amiga-stumpi/funkotto/docs/results/2026-10-10-m4-usb.md

# M4-Konfiguration: USB-Vorbereitung ohne Trägerplatine

Stand 10.10.2026. **Softwareseitig umgesetzt; erster realer USB-Statustest bestanden.**
M0 und aktive M2-Transfers bleiben offen, da noch keine Trägerplatine verfügbar
ist. W5 bleibt ausgelassen. Kein Amiga-Konfigurationsprogramm in diesem Schritt.

## Implementiert

- Gemeinsamer Konfigurationsdispatcher: Fähigkeiten, Status, Scan/Ergebnisse,
  RAM-Profil, Verbinden/Trennen, Speichern/Löschen, asynchrone Auftragsabfrage.
- Separater USB-Modus mit Transportversion 2 und FOC1/API 1.0; bestehende RAW-v1-
  und M2-Diagnoseprotokolle unverändert. Begrenzte COBS-/CRC32-Rahmen, zufällige
  Sitzung, Sequenzen, byteidentischer Replaycache, DTR-/Inaktivitätsende.
- Annahme und Abschluss getrennt; Wiederholung einer verlorenen Antwort löst
  den Auftrag nicht erneut aus. Keine automatische Wiederholung nach Reset oder
  Sitzungsende. CONNECT-OK ist kein LINK_UP-Nachweis; SCAN-OK kein Scanabschluss.
- Python-Werkzeug mit verdeckter Passworteingabe, Fähigkeitenprüfung und JSON-
  Ausgabe ohne Passwort. Keine Passwort-Kommandozeilenoption. Explizites Save
  und Erase; keine automatische Trennung beim Scan.
- Eigenes Ziel `funkotto_m4_usb`, Version `0.1.0-m4-usb`, auf bestehender W4-Basis.
  GPIO-Sperre, W4-Journal und Flash-Speicherlayout erhalten; keine KiCad-Änderung.

## Lokale Nachweise

- Zwölf native C-Testprogramme mit AddressSanitizer/UndefinedBehaviorSanitizer
  bestanden, einschließlich bisheriger WLAN-/Journaltests und der neuen
  Konfigurations-/Konsolenprüfungen. LeakSanitizer lokal wegen eingeschränktem
  /proc-Zugriff deaktiviert; ASan/UBSan bleiben aktiv.
- 29 Python-Unittests bestanden. Zwölf neue Prüfungen verwenden den tatsächlichen
  C-Dispatcher/USB-Parser als Shared Library mit simuliertem WLAN-Service.
  Profil/Connect/Save/Erase, Scan, verzögerter Abschluss/Flashfehler, verlorene
  Antwort, Timeout/Reset ohne erneute Ausführung, BUSY, geänderte Wiederholung,
  Fähigkeiten, CRC/Resynchronisation und Grenzlängen sind abgedeckt.
- C-Prüfungen: Replay vor/nach Auftragsabschluss, Session-/Sequenzfehler,
  Generation/Hidden-SSID, Passwort-Zwischenpufferlöschung, Überlauf, unvollständige
  Rahmen, 50.000 deterministisch erzeugte Streambytes ohne Seiteneffekte.
- Release-Builds für M1, M2 gesperrt, W1/W2, W3, W4 und M4_USB erfolgreich;
  ELF-/UF2-Prüfung für alle sechs Ziele bestanden. M4_USB ohne UART/IP-Stack/
  Parallelport-Aktivierung; flashkritische Funktionen im SRAM. 4-KiB-Core-0-Stack,
  unveränderte zwei Profilsektoren und separate E10-Reservierung geprüft.
- Board-GPIO-/Resetvertrag gegen unverändertes Nutzer-PCB bestanden.

Die Simulation weist keine echte WLAN-Assoziation oder USB-CDC-Timing nach.
DTR, Terminalwechsel und das Zusammenspiel am realen Pico müssen vom Nutzer
geprüft werden. Der neue USB-Modus enthält keine elektrische M0-/M2-Freigabe.
Der exakte Quellstand und die Artefaktprüfsummen stehen im Paketmanifest.
Die [GitHub-CI](https://github.com/amiga-stumpi/funkotto/actions/runs/38085424436)
für Quellstand `e92d982f16d1` ist vollständig erfolgreich abgeschlossen.

## Nutzerprüfung: erster USB-Status (10.10.2026)

Vom Nutzer zurückgemeldet, Windows/COM6, Paket `funkotto-m4-usb-e92d982f16d1`:

```text
python tools/wifi_config.py --port COM6 --report m4-status.json status
```

| Merkmal | Gemeldetes Ergebnis |
| --- | --- |
| Befehlslauf | `stage=M4_USB`, `command=status`, `passed=true` |
| Fähigkeiten | `FOC1`, Version `1.0`, Maske `63`, Payload `128`, Land `DE` |
| WLAN | `LINK_UP`, `error=OK`, `sdk_error=0` |
| Profil | `configured=true`, `stored=true`, `flash_profile=true` |
| Speicher | `storage_state=1` (PROFILE), `flash_ready=true`, `storage_sequence=3`, `storage_error=0` |
| Verbindung | `auto_retry=true`, `attempts=1`, `links=1`, `epoch=2` |
| RSSI | `rssi_valid=true`, `rssi=-46` |
| Scan/Auftrag | `scanning=false`, `sdk_busy=false`, `command_busy=false` |
| USB | `usb_retries=0`, `usb_bad_frames=0` |

SSID `Linux`, MAC `2c:cf:67:e9:c8:b9`, `mac_valid=true`. Scan-Generation,
scan_done und scan_count stehen noch auf 0. Das gespeicherte Profil ist mit
Sequenz 3 weiterhin verfügbar, passend zum zuletzt bestätigten W4-Profil.
Der reale HELLO-/STATUS-Austausch und eine bestehende WLAN-Verbindung sind damit
bestätigt. Neue Konfigurationsänderungen, USB-Scan, Save/Erase und ein separater
M4_USB-Kaltstarttest sind durch diesen lesenden Lauf noch nicht nachgewiesen.
Die Angaben stammen aus der eingefügten Ausgabe; die JSON-Datei selbst wurde
nicht separat hochgeladen oder eingelesen.

## Nutzerprüfung: Disconnect, Scan und Reconnect bestanden (10.10.2026)

Weitere eingefügte Ausgaben aus demselben Paket auf Windows/COM6:

- DISCONNECT: `passed=true`, Job 1 mit `result=OK`; anschließend DISCONNECTED,
  `auto_retry=false`, `epoch=3`. Profil bleibt gespeichert, Sequenz 3.
- SCAN: `passed=true`, Generation 1, `scan_done=1`, fünf Einträge,
  `truncated=false`, `scanning=false`, `sdk_error=0`. Der Scan ist abgeschlossen.
  Zwei Einträge mit SSID `Linux` haben unterschiedliche BSSIDs: Kanal 10,
  RSSI -45, Authwert 5 sowie Kanal 11, RSSI -85, Authwert 7. Das sind getrennte
  BSSIDs, keine doppelte Ausgabe desselben Scan-Eintrags.
- CONNECT: Job 1 mit `result=OK`, `auto_retry=true`, `attempts=2`, `epoch=4`.
  Sofortiger Status CONNECTING, `sdk_busy=true`; eine weitere STATUS-Abfrage
  weiterhin CONNECTING, nun `sdk_busy=false`. `links=1` stammt noch von der
  Verbindung vor DISCONNECT und belegt keinen erfolgreichen Reconnect.
- Alle vier Befehlsläufe melden `passed=true`, `usb_retries=0` und
  `usb_bad_frames=0`; keine Speicherfehler, Profilsequenz unverändert 3.

Eine nachfolgende STATUS-Ausgabe bestätigt den Reconnect: `LINK_UP`,
`error=OK`, `sdk_error=0`, `attempts=2`, `links=2`, `epoch=4`.
RSSI -50 mit `rssi_valid=true`; `sdk_busy=false`, `command_busy=false`.
Profil weiterhin gespeichert, Sequenz 3, `storage_error=0`. Auch diese Abfrage
hat `passed=true`, `usb_retries=0` und `usb_bad_frames=0`.
Damit ist die gesamte Folge Disconnect → Scan → Connect → LINK_UP real bestanden.
Die Zähler zeigen einen zusätzlichen Verbindungsversuch und einen zusätzlichen
Linkaufbau; die genaue Verbindungsdauer wurde nicht gemessen. Während DISCONNECTED/CONNECTING ist
`rssi_valid=false`; der angezeigte RSSI ist dann kein aktueller Messwert.
Jobnummer 1 je Aufruf ist erwartbar, da das Werkzeug jeweils eine neue
USB-Sitzung öffnet. Keine Profiländerung oder Speicheroperation erforderlich.

## Nutzerprüfung: Profileingabe und Verbindung bestanden (10.10.2026)

Der Nutzer hat `set --ssid "Linux"` mit verdeckter WPA2-Passworteingabe,
anschließend CONNECT und STATUS auf demselben Paket/COM6 ausgeführt.

- SET: `passed=true`, Job 1 mit `result=OK`; DISCONNECTED, `configured=true`,
  `auto_retry=false`, `epoch=6`. `stored=true`, Speichersequenz weiterhin 3.
- CONNECT: Auftrag OK, zunächst CONNECTING, `attempts=3`, `epoch=7`.
- STATUS: LINK_UP, `error=OK`, `sdk_error=0`, `attempts=3`, `links=3`, `epoch=7`;
  RSSI -55 mit `rssi_valid=true`. Keine laufenden SDK-/Kommandoaufträge.
- Alle drei Läufe ohne USB-Wiederholungen oder fehlerhafte USB-Rahmen.
  `storage_error=0`, `flash_profile=true`, `flash_ready=true`.

Damit sind die verdeckte Eingabe, SET über USB und die Verbindung mit dem
übergebenen RAM-Profil real bestanden. `stored=true` nach SET ist erwartbar:
Der Service vergleicht RAM-Profil und gespeichertes Profil bytegenau; identische
Daten bleiben als gespeichert markiert. SET selbst schreibt nicht in den Flash.
Dieser Test weist keine Änderung des persistenten Profils nach. Das Passwort
wurde weder zurückgegeben noch ins Repository übernommen.

## Nutzerprüfung: SAVE und Wiederanlauf bestanden (10.10.2026)

Als Antwort auf den SAVE-/Kaltstartablauf wurden drei Ausgaben zurückgemeldet:

- SAVE: `passed=true`, Job 1 mit `result=OK`, `stored=true`, `flash_profile=true`,
  `storage_sequence=3`, `storage_error=0`. Während der Antwort bereits CONNECTING,
  `sdk_busy=true`, `attempts=4`, `links=3`, `epoch=9`.
- Nachfolgender STATUS: LINK_UP, `attempts=4`, `links=4`, `epoch=9`, RSSI -46,
  `rssi_valid=true`. Damit auch Wiederverbindung nach dem SAVE-Ablauf bestätigt.
- Letzter STATUS im angeforderten Kaltstartablauf: LINK_UP, `attempts=1`, `links=1`,
  `epoch=2`, Scan-Generation/scan_done/scan_count wieder 0. Profil `Linux` weiter
  vorhanden und gespeichert, Sequenz 3, `flash_ready=true`, `auto_retry=true`,
  RSSI -45 mit gültigem Messwert. `error=OK`, `sdk_error=0`, `storage_error=0`.
- Alle drei Befehlsläufe: `usb_retries=0`, `usb_bad_frames=0`, `passed=true`.

SAVE mit identischem Profil ist als erfolgreicher, idempotenter Auftrag geprüft;
Sequenz 3 bleibt erwartungsgemäß erhalten. Das ist kein Nachweis eines neuen
Flash-Schreibvorgangs. Die zurückgesetzten Laufzeit-/Scanzähler belegen einen
Neustart mit wiederhergestelltem Profil und erfolgreichem Linkaufbau. Die letzte
Ausgabe wird als Ergebnis des angeforderten Kaltstart-/Autoconnecttests geführt;
Stromunterbrechung und Einschaltzeit wurden nicht separat instrumentiert.

Damit sind HELLO/STATUS, Disconnect, Scan, Connect, SET, idempotentes SAVE und
Wiederanlauf für M4_USB im Nutzerablauf bestätigt. ERASE/Neuanlage über den neuen
USB-Zugang und gezielte Stromausfälle während Flashoperationen bleiben offen;
bestehende W4-Nachweise werden nicht als neue M4_USB-Tests ausgegeben.

## Nächste Schritte

1. Amiga-Konfigurationsclient (68000/V34) mit lokalem Simulationsmodus vorbereiten;
   die bestätigte USB-Basis kann dafür verwendet werden, ohne auf die Platine zu warten.
2. ERASE und Neuanlage über USB bei gewünschtem Löschen separat prüfen; erst damit
   einen neuen persistenten Schreibvorgang über diese Schnittstelle nachweisen.
3. Sobald die Trägerplatine vorliegt, M0 und aktive M2-Tests durchführen und danach
   den Konfigurationsclient an den echten Parallelport anbinden. Die vollständige
   M4-Abnahme einschließlich erweiterter Flash-/Resetprüfungen bleibt offen.

[Plan](../konfigurationsprotokoll-plan.md) ·
[Protokoll](../../protocol/CONFIG.md) · [Anleitung](../../firmware/M4_USB_TEST.md)
