amiga-stumpi/funkotto/docs/results/2026-10-09-m2.md

# M2 – Pico-Transport und Amiga-Diagnose

Stand 09.10.2026: M2 ist **softwareseitig implementiert und lokal geprüft**.
Der Nutzer hat einen erfolgreichen SELFTEST-Lauf auf Amiga 500 mit 68020,
Kickstart 1.3 und Workbench 1.3 zurückgemeldet.
Reale Parallelport-Transfers und Messungen bleiben offen; M2 ist noch nicht
als Hardwaremeilenstein abgenommen.
W5 wurde auf Nutzerwunsch ausgelassen; M0 bleibt vor aktiven Bustests erforderlich.

## Umsetzung

- Eigenes Pico-Ziel `funkotto_m2`, standardmäßig nicht aktivierbar. Separater
  Labor-Build mit zusätzlicher ausdrücklicher USB-Aktivierung; jeder Boot gesperrt.
- PIO/DMA-Transport mit definiertem CIA-Lese-/Schreibhandshake, erstem vorgeladenem
  Lesebyte, OE-Sperre vor Richtungsänderung und Ende erst nach letzter Quittierung.
- Feste 1536-Byte-Diagnoseblöcke, CRC16, geprüfte Längen/Padding, Sitzung,
  Sequenzen, Replay, HELLO/GET_INFO/ECHO/LINK_RESET. Kein Hochgeschwindigkeits-
  Blockmodus, keine Netzwerkintegration und kein SANA-II-Treiber.
- `FunkOttoDiag` als relocierbare HUNK-Datei, reiner 68000-Code, V34-Aufrufe.
  SELFTEST ohne CIA-Zugriff; aktiver RUN nur ausdrücklich, mit Ressourcenbesitz,
  Tick-Zeitgrenzen, Ctrl-C und sicherer Rückgabe. Polling nur im Diagnosetool.
- Keine Änderungen an KiCad, W4-Profilformat oder bestehenden WLAN-Quellen.

## Lokale Prüfungen

- Zehn native C-Testprogramme mit ASan/UBSan bestehen: bisherige M1/WLAN/W3/W4-
  Tests plus M2-Protokoll/Host. Alle 17 bisherigen Python-Tests bestehen.
- Zwei zusätzliche Builds des tatsächlichen Pico-Transportcodes gegen SDK-Fakes
  prüfen Standard-Sperre sowie aktiven Zustandsautomaten: OE-Reihenfolge,
  vorgeladenes erstes Byte, Ressourcen-Rollback, dynamische PIO-Wahl, vorzeitiges
  SEL, Teilantwort, Timeout, ungültiger Request und Rückkehr in den Sperrzustand.
- Die von pioasm 2.2.0 erzeugten Instruktionen laufen in einem kleinen Interpreter:
  1/2/3/1536 Bytes, beide Richtungen, gehaltene Quittung, erstes/letztes Byte,
  FIFO-Stillstand ohne vorzeitige Quittierung oder Datenverlust.
- Die tatsächliche Amiga-HUNK-Datei wird an anderer Basisadresse geladen und
  auf einem Unicorn-68000-Modell ausgeführt. SELFTEST mit 64 ECHOs, RUN mit acht
  ECHOs gegen den nativen Protokollkern über simulierte CIA-Leitungen, belegte
  Ressourcen, Timerkonflikt, fehlender Adapter, Ctrl-C, Argumentprüfung,
  Workbench-Nachrichtenantwort, erhaltene Register/Stack und ungerade Wortzugriffe
  sind geprüft. **OS-Vektoren sind simuliert; dies ist kein OS-1.3-Systemtest.**

Die Tests decken unterschiedliche Grenzen ab: Protokoll, Instruktionsfolge,
Transportcode und 68000-ABI. Sie modellieren weder analoge Signalgüte noch
DMA-Arbitration/CIA-Verzögerungen oder den vollständigen Amiga-Betriebssystembetrieb.

## Build und Auslieferung

Lokale Release-Builds für M1, M2 (gesperrt und Labor), W1/W2, W3 und W4
bestehen. Alle zugehörigen ELF-/UF2-Prüfungen bestehen. Das geprüfte
M2-ZIP enthält 21 vollständig verifizierte Einträge.

Quellstand: [`40d05def4ea8`](https://github.com/amiga-stumpi/funkotto/commit/40d05def4ea85b8c42aa0d0af55377e0d4722755).
Die [GitHub-CI](https://github.com/amiga-stumpi/funkotto/actions/runs/37908258851)
ist **erfolgreich**: Hosttests, Boardvertrag, alle Firmware-Ziele,
M2-Transport-/PIO-Prüfungen, 68000-Build/Emulation, Labor-Build,
ELF-/UF2-Prüfungen, Paketierung und Artefaktupload.

Lokale Auslieferung aus diesem Quellstand:

- Gesperrte `funkotto_m2.uf2`: 71.168 Bytes, SHA256
  `a62d270b127aa08b61c53c9a4ecd9afb6df7499539a3d88ac9f34baff84be049`.
- `FunkOttoDiag`: 13.520 Bytes, SHA256
  `214ef077e72b3c4afdef7f36425c13a74c679219405b4454ac3bfc5e7dd5652a`.

Der letzte HUNK-Lauf nach Eintrag der Quellkennung bestand ebenfalls die
68000-Prüfungen. Eigener Stackverbrauch blieb in den geprüften Pfaden unter
4 KiB; für reale OS-Aufrufe empfiehlt die Anleitung `Stack 8192`.

Pico: unveränderte SDK-/Toolchain-Pins aus `firmware/dependencies.json`.
M2 nutzt 4096 Byte Core-0-Stack, einen dynamisch gewählten reservierten PIO-Block
(30 Instruktionen, ein verwendeter SM) und zwei dynamisch gewählte DMA-Kanäle.
WLAN und Flash-Schreibfunktionen sind im M2-Ziel nicht eingebunden. Die Profile
und der separate E10-Sektor bleiben gemäß ELF-/UF2-Prüfung reserviert.

Amiga: GCC 13.3.0-6ubuntu2~24.04cross1, Binutils 2.42-4ubuntu2.10, freistehender
68000-Build ohne libc, Linux-Runtime oder Amiga-SDK-Binärdateien. Der ELF→HUNK-
Konverter prüft alle Relokationen. OS-Stubs passen Registerargumente und
Zeigerrückgabe an die C-Aufrufkonvention an; Drahtfelder werden auch bei ungeraden
Adressen ausschließlich byteweise geladen/gespeichert.

Das Standard-ZIP enthält ausschließlich die gesperrte M2-UF2, zugehörige
ELF/BIN/MAP-Dateien, `amiga/FunkOttoDiag`, beide Manifeste und Anleitungen/Lizenzen.
Der Paketierer lehnt aktive Laborimages sowie unterschiedliche Quellstände ab
und prüft jeden ZIP-Eintrag bytegenau vor Veröffentlichung.

## Vom Nutzer gemeldeter SELFTEST (09.10.2026)

Zurückgemeldete Ausgabe, für die Lesbarkeit in Zeilen aufgeteilt:

```text
FunkOttoDiag M2 / 68000 / OS 1.3 / polling diagnostic only
source=40d05def4ea8
HELLO session=12340001
ECHO verified count=0x00000040
PASS: local protocol selftest; no CIA access.
```

Der lokale Protokoll-Selbsttest ist damit bestanden: HELLO und 64 geprüfte
ECHOs mit dem ausgelieferten Quellstand. Der SELFTEST verwendet den im Programm
enthaltenen Protokollkern und greift nicht auf CIA, Parallelport oder Pico zu.
`session=12340001` ist die erwartete deterministische Selbsttest-Kennung.

Die Bannerangabe `68000 / OS 1.3` bezeichnet das Buildziel, keine automatische
Erkennung des tatsächlich eingesetzten Systems. Der Nutzer hat das Testsystem
anschließend bestätigt: **Amiga 500, 68020, Kickstart 1.3, Workbench 1.3**.
Damit ist der SELFTEST unter OS 1.3 auf diesem 68020-System bestanden; ein Lauf
auf einer realen 68000-CPU bleibt offen. Der Lauf belegt weder elektrische
Übertragung noch einen bestandenen aktiven M2-Bustest.

## Nächste reale Prüfungen

1. Ergänzender SELFTEST auf einem Amiga mit realer 68000-CPU und OS 1.3.
2. Elektrische M0-Messungen am unveränderten Nutzerboard.
3. Kontrollierter Laborlauf mit aktiver Firmware: zunächst HELLO/64 ECHOs,
   anschließend 100.000 Transfers, Abbruch/Reset in beiden Richtungen und
   Oszillogramme der Übergaben.
4. Erst danach M2-Hardwareabnahme und gemeinsame Integration mit WLAN/Profilen.

[M2-Testanleitung](../../firmware/M2_TEST.md) ·
[Signal-/Rahmenspezifikation](../../protocol/M2.md) ·
[Amiga-Build](../../amiga/diag/README.md)
