amiga-stumpi/funkotto/docs/results/2026-10-09-w4.md

# W4 – Dauerhaftes WLAN-Profil und Autoconnect

Stand 09.10.2026: W4 ist als eigenes Ziel `funkotto_w4` implementiert. Die
W3-Basis (Roh-Ethernet, 1.000 geprüfte Pings und vom Nutzer bestätigte
AP-Wiederverbindung) bleibt erhalten. **Der erste reale W4-Kaltstart mit
automatischer Wiederverbindung ist vom Nutzer ausdrücklich als bestanden
bestätigt.** Der zugehörige Status zeigt ein gültiges gespeichertes Profil
und eine aktive WLAN-Verbindung. Auch der anschließende Löschtest und die
erneute Einrichtung einschließlich Speichern sind durch Nutzerstatus belegt. Die vollständige
Hardwareabnahme bleibt offen.

## Umsetzung

- Zwei reservierte 4-KiB-Sektoren, explizites Format, CRC32, modulare Sequenz
  und gesonderte Commit-Seite. Rücklesen vor Erfolg; identisches Profil ohne
  weitere Flash-Schreibzyklen.
- `wifi save` speichert ausdrücklich. `wifi set` ändert weiter nur RAM.
  Nach Start verbindet das neueste gültige Profil automatisch, ohne USB-Terminal.
- `wifi erase` trennt WLAN, löscht RAM und schreibt zuerst einen Löschdatensatz.
  Alte Flashdaten werden anschließend entfernt. Nach gültigem Lösch-Commit
  kann unterbrochene Bereinigung kein altes Profil aktivieren; Boot setzt sie fort.
- Unbekanntes Format und mehrdeutige Sequenzen werden ohne Autoconnect gemeldet.
  Explizites Löschen erlaubt eine neue Einrichtung. Leerer/beschädigter Speicher
  führt nicht zu einer Bootschleife.
- Core 1 schreibt erst nach WLAN-Deinit, DMA-Ruhe und Prüfung der Bussperre.
  SDK-Multicore-Lockout ist auf beiden Kernen initialisiert; kein geteilter
  Lock wird während Flashoperationen gehalten. Flash-Callback, SDK-Schreib-/
  Löschfunktionen und Lockout-Handler werden im ELF als SRAM-Code geprüft.
- Zusätzlicher Status trennt gespeichertes Profil von abweichendem RAM-Profil.
  Passwörter werden nicht ausgegeben; Speicherung ist unverschlüsselt.
- M1, W1/W2 und W3 bleiben separat baubar. Hardwaredateien unverändert.

## Prüfungen

Hosttests verwenden ASan/UBSan. Neben den bisherigen fünf C-Testprogrammen
kommen Journal-, Flash-Guard-, W4-Service- und W4-Parser-Tests hinzu.
Das Journal wird bei **13.314 Byte-Grenzen** unterbrochen: 4.609 Positionen beim
Ersetzen eines Profils und 8.705 beim Löschen einschließlich Bereinigung.
Zusätzlich werden Erstinstallation in 16-Byte-Schritten, CRC-/Commit-Korruption,
Schemafehler, Sequenzüberlauf/Mehrdeutigkeit, Rücklesefehler und Idempotenz geprüft.

Service-Tests verwenden den tatsächlichen WLAN-Service gegen SDK-/Flash-Fakes:
Speichern, geändertes RAM-Profil, Wiederverbindung, Boot-Autoconnect, Löschen,
Fortsetzung unterbrochener Bereinigung und Schreibverbot ohne Ruhefreigabe.
Backend-Tests prüfen Kernnummer, Bussperre, Opferkern-Initialisierung, DMA-Status,
SRAM-Datenquelle, zulässige Offsets/Seiten und fehlgeschlagenen SDK-Eintritt.
Die bisherigen 17 Python-Tests prüfen weiterhin Rohtransport und Paketierung.

Die Simulation bildet byteweise unterbrochenes NOR-Löschen/Programmieren ab,
keine reale Unterspannung oder beliebige physische Flashschäden. Unterbrechung
vor gültigem Commit kann den alten Stand erhalten; erst bestätigte Befehle sind
als abgeschlossen zu behandeln. Ein SDK-Fehler nach ausgeführtem Callback kann
bereits einen neuen gültigen Datensatz hinterlassen; der Status wird neu geladen.

## Lokales Build-Ergebnis

Alle neun nativen C-Testprogramme mit ASan/UBSan und alle 17 Python-Tests
bestehen. Release-Builds für M1, W1/W2, W3 und W4 bestehen mit der festgelegten
Toolchain und den unveränderten SDK-Pins. Die vier ELF-/UF2-Prüfungen bestätigen
Profil-/E10-Reservierung und fehlende UART-Einbindung; WLAN-Ziele enthalten kein
lwIP. W4 prüft zusätzlich die Flash-kritischen Funktionen im SRAM.
Hardware-Pinvertrag und unverändertes Nutzer-PCB stimmen überein.
Das W4-ZIP enthält 22 bytegenau verifizierte Einträge. Ein realer Pico-Flashvorgang
wurde in dieser Entwicklungsumgebung nicht ausgeführt.

Firmware-Quellstand:
[`229dfaacaf10`](https://github.com/amiga-stumpi/funkotto/commit/229dfaacaf108cbaa65ef3642edf518aa49c6b15).
[GitHub-CI](https://github.com/amiga-stumpi/funkotto/actions/runs/37902238647)
ist **erfolgreich**: Hosttests, Hardwarevertrag, alle vier Firmware-Builds,
ELF-/UF2-Prüfungen, Paketierung und Artefaktupload.

Lokale W4-UF2 aus diesem Quellstand: 595.456 Bytes, SHA256:
`386412f41eb851570c319d267292e420ce99cb8bfcce979476165ac4636550fe`.
Der separate Download und die UF2 im ZIP werden bytegenau verglichen.

## Erster realer W4-Status (09.10.2026)

Vom Nutzer übermittelte Statusfelder (MAC und SSID hier ausgelassen):

```text
wifi=LINK_UP error=OK sdk_error=0 configured=1 stored=1 auto_retry=1 sdk_busy=0
rssi_valid=1 rssi=-37 attempts=3 links=1 epoch=6 retry_at_ms=0
last_link_error=-1 failed_attempt=2
storage=PROFILE storage_error=0 flash_profile=1 flash_ready=1 storage_seq=1
```

- `storage=PROFILE`, `flash_profile=1` und `storage_seq=1` melden einen gültigen
  gespeicherten Profildatensatz. `stored=1` bestätigt, dass das aktuelle RAM-Profil
  mit diesem Datensatz übereinstimmt. Es wird kein Speicherfehler gemeldet.
- `LINK_UP`, `error=OK` und gültiger RSSI bestätigen die aktive WLAN-Verbindung.
  Nach zwei fehlgeschlagenen Versuchen gelang der dritte Verbindungsversuch.
- `last_link_error=-1` (`JOIN_FAILED`) und `failed_attempt=2` sind historische
  Diagnosewerte des zweiten Versuchs, kein aktueller Verbindungsfehler.
- Der Nutzer hat anschließend ausdrücklich bestätigt: „Ja, der Kaltstart mit
  automatischer Wiederverbindung ist bestanden“. Damit ist der erste Kaltstart
  nach vollständigem Stromverlust ohne geöffnetes Terminal als bestanden
  dokumentiert: Das gespeicherte Profil wurde geladen und WLAN automatisch
  wieder verbunden. Grundlage sind die Statusausgabe und die Nutzerbestätigung;
  eine Serie mehrerer Kaltstarts ist damit noch nicht belegt.

## Löschtest und erneute Einrichtung (09.10.2026)

Als Antwort auf den Testablauf `wifi erase`, Erfolg abwarten, stromlos machen,
neu starten und Status prüfen übermittelte der Nutzer:

```text
wifi=UNCONFIGURED error=OK configured=0 stored=0 auto_retry=0
attempts=0 links=0 epoch=0
profile_ssid_len=0 last_link_error=0 failed_attempt=0
storage=DELETED storage_error=0 flash_profile=0 flash_ready=1 storage_seq=2
```

Damit ist der Löschtest im beschriebenen Neustartablauf bestanden: kein geladenes
Profil, kein automatischer Verbindungsversuch und kein Speicherfehler.
`DELETED` bezeichnet den gültigen Löschdatensatz, dessen Sequenz gegenüber dem
vorherigen Profil von 1 auf 2 gestiegen ist.

Die anschließende erneute Einrichtung und Verbindung gelang beim ersten Versuch:

```text
wifi=LINK_UP error=OK configured=1 stored=0 auto_retry=1
rssi_valid=1 rssi=-39 attempts=1 links=1 epoch=3
storage=DELETED storage_error=0 flash_profile=0 flash_ready=1 storage_seq=2
```

Das neue Profil liegt an diesem Punkt erwartungsgemäß nur im RAM. `wifi set`
und `wifi connect` überschreiben den Löschdatensatz nicht. Auf
`wifi command=3 result=OK` folgt eine weitere vom Nutzer übermittelte Statusausgabe:

```text
wifi=LINK_UP error=OK sdk_error=0 configured=1 stored=1 auto_retry=1
rssi_valid=1 rssi=-47 attempts=1 links=1 epoch=2 retry_at_ms=0
last_link_error=0 failed_attempt=0
storage=PROFILE storage_error=0 flash_profile=1 flash_ready=1 storage_seq=3
```

Damit ist auch das erneute Speichern nach dem Löschen bestätigt: gültiges
Flashprofil, Übereinstimmung mit dem aktiven RAM-Profil und kein Speicherfehler.
Die Folge Profil (Sequenz 1), Löschdatensatz (2), neues Profil (3) ist durch die
Statusausgaben belegt. WLAN ist beim ersten Versuch verbunden. Die geänderte
`epoch` allein wird nicht als zusätzlicher Kaltstartnachweis gewertet.

Die grundlegende W4-Funktionsprüfung auf dem Pico ist damit bestanden:
Speichern, bestätigter Kaltstart mit Autoconnect, Löschen im beschriebenen
Neustartablauf sowie erneutes Einrichten, Verbinden und Speichern.

Wiederholte Kaltstarts, Profilerhalt beim Firmwareupdate und unterbrochene
Flashoperationen auf realer Hardware bleiben offen.

## Hardwareabnahme

[W4-Testablauf](../../firmware/W4_TEST.md): neu konfigurieren, `wifi save`,
auf `result=OK` warten, vollständiger Stromverlust, Start ohne geöffnetes Terminal,
`wifi status` prüfen und Rohpakettest wiederholen. Danach `wifi erase` und
Neustart ohne Profil prüfen. Zunächst drei Kaltstarts; weitergehende Abnahme
100 Kaltstarts, fehlender AP, Update-Erhalt sowie unterbrochene Flashoperationen.

SANA-II, aktive Parallelport-Kommunikation, elektrische M0-Abnahme und
Langzeit-/Latenzuntersuchung bleiben separate Schritte. Die Firmware hält
`bus_locked=1` und `output_mask=0x00700000`.

[Format und Sicherheitsmechanismus](../../firmware/PROFILE_FORMAT.md).
