amiga-stumpi/funkotto/docs/results/2026-10-09-w3.md

# W3 – Implementierung und Prüfstand, 09.10.2026

W3 ist als eigenes Firmwareziel `funkotto_w3` implementiert. Die bisherige
W1/W2-Firmware bleibt separat baubar. **Der erste echte ARP/ICMP-Test am Pico
ist am 09.10.2026 bestanden:** Der Nutzer hat unter Windows über COM6 zwölf
geprüfte Echo-Antworten ohne Paketverlust zurückgemeldet. Der anschließende
1.000-Ping-Lauf ist ebenfalls bestanden und anhand von JSON und PCAP geprüft.
AP-Ausfall mit Wiederverbindung und anschließend erneutem Pakettest wurde
vom Nutzer ebenfalls als erfolgreich bestätigt. Langzeitbetrieb und weitere
Belastungstests bleiben offen.

## Änderungen

- Je acht feste TX/RX-Puffer à 1600 Bytes, maximal 1514 Ethernet-Bytes ohne FCS.
- TX-Quell-MAC-Prüfung, Ethernet-II-Prüfung und Nullpadding auf 60 Bytes.
- Core 1 besitzt CYW43 inklusive Sendefunktion; RX kopiert vor Callback-Ende.
- Explizite BUSY-/Drop-/Abbruchzähler, FIFO-Reihenfolge und getrennte Lebensdauer
  von Warteschlange, SDK-Aufruf und abgeholtem TX-Abschluss.
- Link-/Sitzungswechsel bereinigen alte Aufträge. Eine verspätete SDK-Rückkehr
  kann keinen neuen Slot überschreiben. SDK-Erfolg ist keine Zustellbestätigung.
- USB-Testmodus `raw on`: COBS, CRC32, Sitzungsschlüssel, Sequenz und gespeicherte
  Antwort für sichere Wiederholung. DTR Low kehrt zur normalen Konsole zurück.
- Python-Werkzeug für freie Test-IP, ARP, ICMP mit Nutzdatenprüfung, PCAP und JSON.
- W3 in CI, ELF/UF2-Manifest und ZIP-Paketierung aufgenommen. ZIP wird vollständig
  im Speicher abgeschlossen, inhaltlich geprüft, atomar geschrieben und erneut
  bytegenau verifiziert; manifestwidrige Artefakte werden nicht verpackt.

## Automatisierte Prüfungen

Native C-Tests mit AddressSanitizer/UndefinedBehaviorSanitizer:

- Bisherige M1-, WLAN-Parser-/Zustandsautomaten- und echte Service-Tests.
- W3-Pufferbesitz nach Änderung des Eingabepuffers, Mindest-/Maximallänge,
  volle TX-/RX-Ringe, wiederholter Ringumlauf, Padding und FIFO-Reihenfolge.
- Linkverlust, Epochenwechsel, neue USB-Sitzung und verspäteter Sendefertigmeldung.
- CRC-Testvektor, COBS-Grenzlängen, falsche CRC, Session/Sequenzfehler,
  identische Wiederholungen vor/nach TX-Abschluss sowie RX-Wiederholung.
- Übergroßer Datenstrom und 200.000 deterministisch erzeugte Störbytes mit
  anschließender erfolgreicher Resynchronisation.
- Tatsächlicher W3-Service gegen SDK-Fake: TX-Aufruf ohne gehaltene Sperre,
  reentrant aufgerufener RX-Callback, Kopierdauer und Linkverlust vor Sendung.

Python-Tests prüfen das PC-Werkzeug direkt gegen die kompilierte C-Protokoll- und
Pufferimplementierung: abgeschnittene HELLO/TX/RX-Antworten werden wiederholt,
ohne doppelte Sendung/RX-Entnahme. Hinzu kommen ARP, ICMP-Prüfsummen, Adressen,
Sequenzen/Nutzdaten, Konflikterkennung, ARP-Antworten und PCAP-Aufbau.

## Build-Ergebnis

Lokaler Release-Build für Pico 2 W / RP2350 Arm mit den festgelegten SDK-/Treiber-
und Toolchain-Versionen erfolgreich. Alle fünf nativen Testprogramme mit ASan/UBSan
und 17 Python-Tests bestehen; Hardware-Pinvertrag stimmt mit dem Nutzer-PCB überein.
M1-, W1/W2- und W3-ELF/UF2-Prüfung bestätigen die getrennten Flashbereiche und
fehlende UART-Einbindung. W3 bindet weder lwIP noch DHCP ein. Der SDK-pbuf-Zweig
wird ausschließlich durch einen Fehler-Guard erfüllt; alle Sendungen verwenden
`is_pbuf=false`. Es gibt keine SDK-Quelländerungen.

Der eigene Release-Quellcode wird mit Warnungen als Fehler gebaut. Core 0 behält
seinen 4-KiB-Stack in der Scratch-Bank; Paketarbeitsbereiche sind statisch.
Core 1 behält den expliziten 8-KiB-Stack. Artefaktgrößen, Hashes und konkreter
Quellcommit stehen im mitgelieferten Manifest.

Firmware-Quellstand: [`b09aa6182ef8`](https://github.com/amiga-stumpi/funkotto/commit/b09aa6182ef814f4965a1bd229d03698d7e88c7d).
[GitHub-CI für diesen Commit](https://github.com/amiga-stumpi/funkotto/actions/runs/37897967381)
ist **erfolgreich**: Hardwarevertrag, Hosttests, alle drei Firmwareziele,
Artefaktprüfungen, ZIP-Paketierung und Upload.

Die lokal aus diesem Quellstand gebaute W3-UF2 ist 585.728 Bytes groß, SHA256:
`b655c34715b19611c58d3c50cd730697e5d13c5ff06ceb72f457ee2298a72ab8`.
Das ZIP enthält UF2, ELF, Map, BIN, Manifest, PC-Werkzeug, Anleitungen und
Lizenzhinweise. Alle 20 Einträge werden bytegenau geprüft.

## Erster realer W3-Test – Nutzerrückmeldung vom 09.10.2026

Getestet mit dem bereitgestellten Paket `funkotto-w3-b09aa6182ef8` unter Windows,
USB-Port COM6. Grundlage ist die vom Nutzer übermittelte Konsolenausgabe;
die erzeugten Dateien `w3.pcap` und `w3.json` wurden nicht separat eingesehen.

| Prüfung | Ergebnis |
| --- | --- |
| USB HELLO / STATS | erfolgreich, gültige Stations-MAC, Link aktiv |
| WLAN-Link-Epoche | unverändert 3 während beider Läufe |
| ARP-Auflösung | Gegenstelle antwortet |
| ICMP-Echo | 12 gesendet, 12 empfangen, 0 verloren |
| ICMP-Nutzdaten | 0, 56, 512, 1472 Bytes, jeweils dreimal; alle `verified=1` |
| Maximaler Frame | 1514 Bytes ohne FCS / IPv4-MTU 1500 erfolgreich |
| TX | 16 eingereiht, 16 vom SDK angenommen, 0 Fehler/Abbrüche/BUSY/ungültige Frames |
| RX während Pakettest | 16 zusätzlich eingereiht (Zähler 1 → 17), 0 Überläufe/ungültige Frames |
| USB | 0 Wiederholungen; Firmware: 0 fehlerhafte Frames und 0 Sequenzfehler |
| Puffer am Testende | TX 0, RX 0; bisherige Höchstbelegung jeweils 1 |

Die 16 TX-Frames passen zu drei ARP-Adressproben, einer ARP-Auflösung und zwölf
ICMP-Anfragen. Die Echo-Prüfung belegt den funktionierenden Rohdatenpfad in
beide Richtungen einschließlich Ethernet-Mindestlänge und MTU-Grenze. Der
PC sendet kurze Frames bereits auf 60 Bytes aufgefüllt; der zusätzliche
Padding-Zweig der Firmware wurde damit nur in den automatisierten Tests geprüft. Der
vorherige reine Statusaufruf hatte noch keine TX-Pakete gesendet; sein
`passed=true` allein wäre kein LAN-Paketnachweis gewesen.

Gemeldete RTT: 0 bis 78 ms, Mittelwert ca. 33,83 ms. Sie enthält PC, USB und WLAN
und ist kein Amiga-Durchsatzwert. Die sichtbare Zeitquantisierung und `0.00 ms`
erlauben keine Aussage über die tatsächliche minimale Funklatenz.

### Einmaliger Host-Zähler `usb_bad_frames=1`

Beide Aufrufe melden hostseitig genau einen fehlerhaften Frame, ohne Wiederholung.
Die Ursache lässt sich aus dem Übergang zum Binärmodus reproduzieren:
`main_wifi.c` gibt vor dessen Aktivierung die ASCII-Zeile `RAW v1; ...` aus;
`wifi_diag.py` führt diese Textbytes bis zum ersten Null-Delimiter zunächst dem
COBS-Decoder zu. Dabei erhöht es seinen Sammelzähler `bad_frames`. Dieser zählt
auch ungültige Text-/Framingdaten, nicht ausschließlich CRC-Fehler.

Ein lokaler Nachstelltest mit dieser Begrüßung vor dem tatsächlichen
C-Protokollcode erzeugt genau `usb_bad_frames=1`, `usb_retries=0` und gültige
HELLO-/STATS-Antworten. Somit ist der hier beobachtete einzelne Startzähler
kein Hinweis auf verlorene Ethernet-Pakete. Weitere Fehler während der Sitzung
wären gesondert zu untersuchen. Eine getrennte Zählung der Startbegrüßung ist
eine mögliche spätere Verbesserung des PC-Werkzeugs; keine neue Firmware ist
für diesen erfolgreichen Test erforderlich.

`rx_inactive=127` zählt vor dem aktiven Pakettest verworfene Frames und bleibt
währenddessen unverändert. `rx_flushed=1` passt zum beim ersten Statusaufruf
wartenden RX-Frame, der beim Beenden jener Sitzung entfernt wurde.

## Reale Folgeprüfung – 1.000 Pings, 09.10.2026

Der Nutzer hat `w3-1000.json` und `w3-1000.pcap` bereitgestellt. Beide Dateien
wurden vollständig gelesen. Der PCAP-Container ist vollständig: 2.054 Ethernet-
Datensätze ohne abgeschnittene Records oder gekürzte Frames. Der Mitschnitt
umfasst rund 32,786 Sekunden einschließlich ARP-Vorlauf; damit ist dies ein
wiederholter Funktionstest, noch kein stundenlanger Dauerlauf.

| Prüfung | Ergebnis |
| --- | --- |
| JSON-Gesamtergebnis | `passed=true`, 1.000 gesendet, 1.000 empfangen, 0 verloren |
| PCAP-Echo-Paare | 1.000 Anfragen und 1.000 passende Antworten, Sequenzen 1–1.000 |
| Duplikate | keine doppelten Echo-Anfragen oder -Antworten |
| Nutzdatenlängen | 0, 56, 512 und 1472 Bytes, jeweils 250 Paare |
| Inhaltsprüfung | Alle Paare: MAC-/IP-Adressen, IPv4-/ICMP-Prüfsummen, Kennung, Sequenz und exakte Nutzdaten korrekt |
| Framegrenzen | TX-Länge jeweils `max(60, 42 + ICMP-Nutzdatenlänge)`; maximal 1514 Bytes ohne FCS |
| TX-Zählerdifferenz | +1.004 eingereiht, +1.004 erfolgreich: drei ARP-Probes, eine ARP-Auflösung, 1.000 Echo-Anfragen |
| RX-Zählerdifferenz | +1.049 eingereiht; zusätzlich ein beim Start wartender Frame; 1.050 RX-Records im PCAP |
| TX-/RX-Fehler | kein TX-Fehler, Abbruch, BUSY, ungültiger Frame oder RX-Überlauf |
| Link | aktiv; Epoche unverändert 3 |
| Puffer | zum Ende beide leer; Höchstbelegung TX 1 / RX 2 von jeweils 8 |
| USB | keine Wiederholung, keine Firmware-Framing-/Sequenzfehler; bekannter Host-Startzähler weiterhin 1 |

PCAP und Bericht stimmen bezüglich TX-/RX-Anzahl überein. Die zusätzlichen
RX-Pakete neben den Echo-Antworten sind im Mitschnitt vorhanden und stellen
keinen Verlust oder zusätzliche Ping-Antworten dar. `rx_inactive` und
`rx_flushed` ändern sich während des Laufs nicht.

### Laufzeiten und Ausreißer

Der JSON-Bericht nennt eine vollständige RTT von durchschnittlich **29,5 ms**,
maximal **1.000 ms**. Die PCAP-Zeitdifferenz vom erfassten TX-Frame zur passenden
Antwort beträgt im Mittel 17,112 ms, Median 12,565 ms, 95. Perzentil 31,992 ms
und 99. Perzentil 57,105 ms (Perzentile nach aufsteigender Rangposition).
Die größten Differenzen sind:

| Echo-Sequenz | ICMP-Nutzdaten | PCAP-Zeitdifferenz |
| --- | --- | --- |
| 872 | 1472 Bytes | 985,263 ms |
| 887 | 512 Bytes | 613,995 ms |
| 987 | 512 Bytes | 301,076 ms |

Auch diese Antworten kamen korrekt und innerhalb des Testzeitlimits an.
Die Ausreißer sind ein offener Messpunkt, kein Paketverlust. Die Ursache lässt
sich hier nicht zwischen PC-Scheduling, USB, WLAN und Gegenstelle aufteilen.
PCAP-TX wird erst nach SDK-Annahme erfasst, während die JSON-RTT schon vor dem
USB-Sendeauftrag beginnt; die Messwerte sind daher nicht direkt gleichzusetzen.
Zusätzlich verwenden die beiden Messungen unterschiedliche Host-Zeitquellen.
Weder der Mittelwert noch `0.00 ms` im JSON sind eine reine Funklatenz oder ein
Amiga-Durchsatzbenchmark. Der Mitschnitt stammt vom USB-Testclient, nicht von
einer unabhängigen LAN-Gegenstelle.

### Zuordnung der geprüften Originaldateien

- `w3-1000.json`, SHA256:
  `c324d77cfaf65e0e130c4af29604b158a7778b21eaa30404343dd031858b456f`
- `w3-1000.pcap`, SHA256:
  `ae9c1cda8e5bb1ca08cea1e67dd8991373a99349f6ddb4711513dde2380c7df4`

Die Originaldateien werden durch diese Dokumentation nicht verändert.

## AP-Ausfall und Wiederanlauf – Nutzerrückmeldung vom 09.10.2026

Auf den angeleiteten Test (AP während des Pakettests ausschalten, wieder
einschalten, auf `LINK_UP` warten und den Pakettest in einer neuen Sitzung
starten) hat der Nutzer mit „das hat funktioniert“ geantwortet.
Damit sind AP-Ausfall, Wiederverbindung und anschließender erneuter Paketbetrieb
als erfolgreiche Nutzer-Hardwareprüfung dokumentiert. Für diesen zusätzlichen
Versuch wurden keine neuen Logs, JSON-Berichte oder PCAP-Dateien übermittelt;
Reaktionszeiten, genaue Fehlerausgabe, Paketanzahl und Zählerverläufe sind daher
nicht separat verifiziert. Die zuvor geprüften 1.000er-Dateien stammen aus dem
ungestörten Lauf und werden nicht als Mitschnitt des Ausfalltests gewertet.

## Grenzen und nächster Schritt

Der reale bidirektionale Basisnachweis und der 1.000-Ping-Test sind erbracht;
der Ausfall-/Wiederanlauftest ist durch den Nutzer bestätigt. Damit ist die
W3-Funktionsbasis für den nächsten Entwicklungsschritt W4 vorhanden: dauerhaftes
WLAN-Profil und automatischer Verbindungsaufbau nach Stromverlust.
Die weitergehenden Prüfungen bleiben eigenständige offene Punkte.
Volle Ringe wurden automatisch geprüft, aber in den realen Läufen noch nicht
belastet (Höchstbelegung TX 1 / RX 2). Die beobachteten Latenzausreißer und ein
längerer Dauerlauf bleiben offen. Ein unabhängiger LAN-Mitschnitt und
zusätzliche elektrische M0-Messungen liegen weiterhin nicht vor.
W4 (dauerhaftes WLAN-Profil), SANA-II und Parallelport sind noch nicht implementiert.

Hardwaredateien unverändert; erwarteter PCB-SHA256:
`b2f32df78c15e37ceb1bc0433f0356848106e7a86a1e82df63c3da5a7e26928c`.
GP21/22 bleiben Low, GP20 High, alle anderen Adapterpins Eingang;
`output_mask=0x00700000`. Profilsektoren werden nicht beschrieben.
