amiga-stumpi/funkotto/docs/results/2026-10-08-wlan-w12.md

# WLAN W1/W2 – Implementierungs- und Prüfbericht

Stand: 08.10.2026, Version `0.1.0-w12`. Bezug: [WLAN-Plan](../wlan-entwicklungsplan.md).

## Umgesetzt

- Pico SDK 2.2.0 mit CYW43-Commit `dd7568229f3bf7a37737b9e1ef250c26efe75b23`,
  festgelegten WLAN-Firmware-/NVRAM-Quelldaten und Manifest-Prüfsummen.
- WLAN auf Core 1 im Poll-Kontext ohne lwIP/Bluetooth; USB und Adapter-GPIOs auf Core 0.
- Eigene Link-/Ethernet-Callbacks ersetzen die SDK-Standard-Stubs.
- Länderkennung DE, Scan mit maximal 32 BSSIDs, WPA2-Personal mit RAM-Profil,
  authentifizierter Linkstatus, RSSI, Diagnosezähler und Wiederverbindung.
- USB-Eingabe mit separater SSID-/Passwortabfrage, SSID-Hexmodus, Grenzen,
  Ctrl-C/Timeout/USB-Trennungsabbruch. Passwort erscheint nicht in Ausgaben.
- Eine begrenzte Auftragsmailbox; Zugangsdatenkopie nach Übernahme gelöscht.
- 15-s-Joinfrist, Wiederholung 1/2/4/8/16/30 s. Vor jedem Versuch wird der
  Funkchip neu initialisiert, um alte Firmware-Ereignisse zu verwerfen.
- Core-1-Lebenszeichen steuert das Füttern des 8-s-Hardwarewatchdogs durch Core 0.
- M1 bleibt als separates Diagnoseziel; beide Targets behalten die Bussperre.

## Prüfungen

| Prüfung | Ergebnis |
| --- | --- |
| Bisherige M1-GPIO-/Parsertests | bestanden |
| WLAN-Parser: Grenzen, Leerzeichen, Hex-SSID, Geheimniskopien, Abbruch, 100.000 Zufallsbytes | bestanden, ASan/UBSan |
| Zustandsmodell: kein Profil, Timeout, alte Ereignisse, Linkverlust, Backoff bis 30 s, Disconnect | bestanden, ASan/UBSan |
| Core-1-Service mit SDK-Fake: Scanüberlauf/Deduplikation/Timeout/Abbruch, Mailbox, WPA2-Aufruf, Linkereignisse, Init-Fehler | bestanden, ASan/UBSan |
| Watchdog-Lebenszeichenprüfung einschließlich 32-Bit-Timerüberlauf | bestanden; kein Hardware-Reset simuliert |
| Sechs UF2-Fehlertests | bestanden |
| Adapter-Pinvertrag gegen unverändertes Nutzer-PCB | bestanden |
| Arm-Release-Build M1 und W1/W2 | bestanden |
| Starke Callback-Symbole, kein lwIP/UART, ELF-/UF2-Flashgrenzen | bestanden |
| Reales WLAN: Scan und erster authentifizierter Join | am 08.10.2026 durch Nutzer bestätigt; Details unten |
| AP-Ausfall und automatische Wiederverbindung | am 08.10.2026 durch Nutzer bestätigt; Details unten |
| USB-Latenz unter Last, echte Watchdog-Auslösung, Dauerlauf | noch nicht nachgewiesen |

Die lokalen Sanitizerläufe verwenden wie M1 `ASAN_OPTIONS=detect_leaks=0` wegen
des eingeschränkten `/proc`-Zugriffs; AddressSanitizer und UBSan bleiben aktiv.
Die SDK-Fakes prüfen unsere Serviceabläufe, nicht den realen CYW43-Funkchip oder
Inter-Core-Timing auf RP2350. Die reale M1-Bestätigung ist kein WLAN-Testnachweis.

Kandidatenbuild `w12-candidate-20261008`: Firmware-Ende `0x10045720`, UF2-
Anwendungsbereich bis exklusiv `0x10045800`; dazu der reservierte E10-Block bei
`0x103FDF00`. Beide Profilsektoren ab `0x103FE000` bleiben unberührt.
Arm-size: text 290.588 Byte, data 0, bss 25.212 Byte; text enthält auch RAM-Code
und ist deshalb nicht gleich der Flashspanne. Core 0 reserviert 4 KiB Stack;
Core 1 nutzt zusätzlich einen eigenen 8-KiB-Stack im SRAM. Laufzeit-Spitzenwerte
und tatsächlich belegte PIO-/DMA-Ressourcen sind am Muster zu erfassen.
Ein anschließender Build mit Commit-Kennung kann Größe/Prüfsummen ändern;
maßgeblich ist das Manifest des jeweiligen Pakets.

## Abweichungen und offene Stufen

Das SDK-Adapter- und Core-1-Modul heißt zunächst `wifi_service.c`; der reine
Zustandsautomat liegt in `wifi_model.c`. Eine einzelne Mailbox statt einer
mehrgliedrigen Steuerqueue begrenzt offene Aufträge ausdrücklich auf einen.

W1/W2 enthalten noch keinen TX/RX-Transport: empfangene Frames werden gezählt
und verworfen. Es gibt weder DHCP auf dem Pico noch eine Amiga-Netzwerkfunktion.
Flashprofile und automatisches Verbinden nach Stromverlust folgen erst in W4.
`wifi disconnect` erhält nur das RAM-Profil; ein Stromausfall löscht es.

Die zentrale Watchdog-Entscheidung erlaubt 5 s ohne Core-1-Fortschritt, während
Initialisierung 15 s, danach läuft die 8-s-Hardwarefrist aus. Diese begrenzte
Initialisierungsfrist ist vorläufig und anhand realer `init_ms`/Fehlertests zu
prüfen. Keine Behauptung einer gemessenen WLAN-Startzeit oder eines vollständig
nichtblockierenden SDKs. Vollständiger Treiberneustart pro Versuch ist bewusst
zunächst einfacher zu prüfen; Performanceoptimierung folgt später.

Nächster Schritt: [WLAN-Testanleitung](../../firmware/WLAN_TEST.md) am einzelnen
Pico ausführen und Ausgaben von `info`, `status`, `wifi status`, `wifi stats`
festhalten. M0 bleibt vor aktiven Bustests offen; W3–W5 bleiben ausstehend.

## GitHub-CI und ausgelieferter Build

Quellcommit: `f084b97f2ef71bf3d53e1379e1bb3520c32060cf`.
[GitHub Actions 37838027071](https://github.com/amiga-stumpi/funkotto/actions/runs/37838027071)
ist erfolgreich: Hosttests, Pinprüfung, beide Arm-Builds, Artefaktprüfung,
Paketierung und Upload. Der Lauf nutzt einen frischen GitHub-Checkout.

Lokal ausgelieferte W1/W2-UF2 mit Quellkennung `f084b97f2ef7`:

- Größe: 569.856 Byte.
- SHA-256: `90a83f1c2ea563339b669f4ddfe6bf90fb740b1f56dbf9bb16108267d5a5a454`.
- Firmware-Ende im ELF: `0x10045718`; UF2-Anwendungsbereich bis `0x10045800` exklusiv.
- Manifest enthält zusätzlich Artefakt-, Quellen- und Funkfirmware-Prüfsummen.

Die Prüfsumme bezeichnet den lokalen Downloadbuild; sie ist kein behaupteter
Vergleich mit dem CI-Binary. Der Funk-/Pico-Test bleibt trotz erfolgreicher CI offen.

## Nutzerbefund und Diagnosekorrektur W12.1

Der Nutzer hat mit `f084b97f2ef7` reale Scans mit drei beziehungsweise fünf
Ergebnissen bestätigt, jeweils ohne Scanfehler oder Überlauf. RAM-Konfiguration
und wiederholte Join-Versuche laufen; ein authentifizierter Link ist noch nicht
nachgewiesen (`links=0`). Nach rund 113 s Laufzeit: weiterhin gesperrter Bus,
kein Watchdog-Neustart, WLAN-Initialisierung 731 ms, Core-1-Lebenszeichen 1 ms alt.
Die gemeldeten PIO-/DMA-Masken von null passen zur bereits erfolgten
Treiber-Deinitialisierung während `RETRY_WAIT`.

Zunächst wurde `NONET`, später `DRIVER` bei `sdk_error=0` gemeldet. Der bisherige
Service fasst `CYW43_LINK_FAIL` (-1) unter `DRIVER` zusammen; der erfolgreiche
SDK-Aufruf und ein späterer negativer Linkstatus sind unterschiedliche Ergebnisse.
Die Ziel-SSID wurde im Status bisher nicht ausgegeben. Die Ursache des fehlenden
Links ist damit noch nicht eindeutig bestimmt. WLAN-Namen und MAC-Adressen aus
dem Nutzerprotokoll werden hier nicht veröffentlicht.

W12.1 ergänzt `JOIN_FAILED`, den erhalten bleibenden negativen SDK-Linkstatus
mit Versuchsnummer sowie die übernommene SSID als maskierten Text/Hexbytes und
Länge. Passwörter werden weiterhin nicht ausgegeben. Der Service-Regressionstest
prüft nun ausdrücklich den Fall SDK-Rückgabewert 0 plus Linkstatus -1, das
Beibehalten der Fehlerdiagnose und das Zurücksetzen bei neuem Profil.
Es wird keine bereits bestätigte Behebung des Join-Problems behauptet.

## Erfolgreicher WLAN-Hardwaretest am 08.10.2026, 23:22 Uhr (Europe/Berlin)

Der Nutzer meldet nach Einsatz der W12.1-Diagnose erstmals einen authentifizierten
WLAN-Link. Eine erneute `info`-Ausgabe ist in diesem Protokoll nicht enthalten;
die Zuordnung zu W12.1 folgt dem Testverlauf und den zusätzlichen Diagnosefeldern.
SSID/BSSID/MAC werden im öffentlichen Bericht ausgelassen.

| Messwert | Nutzerbefund |
| --- | --- |
| WLAN-Zustand | `LINK_UP`, `error=OK`, `sdk_error=0` |
| Versuche / erfolgreiche Links | `attempts=1`, `links=1` |
| Konfiguration | RAM-Profil vorhanden, `stored=0` |
| Signal | Scan −35 dBm, verbunden −40 dBm, `rssi_valid=1` |
| Initialisierung | `init_ms=730` |
| Join | `join_ms=2679` |
| Core-1-Lebenszeichen | 1 ms alt |
| Empfang | `rx_dropped_w12=30`, `rx_invalid=0` |
| PIO-/DMA-Belegung | `pio_sm_mask=0x00000100`, `dma_mask=0x00000003` |
| Letzter negativer Linkstatus | `last_link_error=0`, `failed_attempt=0` |

Die 30 gezählten Frames wurden vom Empfangs-Callback angenommen und in W1/W2
absichtlich verworfen. Das belegt Callback-Aktivität mit akzeptierter Länge und
STA-Schnittstelle, noch keinen geprüften Ethernet-Inhalt oder Ende-zu-Ende-Transport.
Die Ressourcenmasken entsprechen PIO2/SM0 und DMA0/1 nach aktueller Bitkodierung.
Init- und Joinwerte sind Firmware-Zeitmessungen dieses Versuchs, keine Messung
Versorgung-an bis Netzwerkbereitschaft und keine statistisch abgesicherte Startzeit.

Gegenüber dem fehlgeschlagenen Versuch haben sich neben der Signalstärke auch
BSSID, Kanal (11 → 10) und Scan-Auth-Kennung geändert. Deshalb ist die zuvor
schwache Empfangssituation eine mögliche Erklärung, aber nicht als alleinige
Ursache bewiesen. Ein kontrollierter Vergleich desselben AP bleibt gegebenenfalls nötig.

Nächste W2-Prüfung: manuelles Disconnect/Connect mit erhaltenem RAM-Profil,
danach AP aus/an und automatische Wiederverbindung. W3 folgt mit echtem
Rohframe-TX/RX und Inhaltsprüfung; W4 ergänzt dauerhafte Profile. Elektrische
M0-Abnahme und aktive Amiga-Kommunikation bleiben offen.

## Manueller Wiederverbindungstest am 08.10.2026, 23:24 Uhr (Europe/Berlin)

Der Nutzer hat ohne Stromunterbrechung `wifi disconnect` und danach
`wifi connect` ausgeführt. Beide Aufträge wurden mit `result=OK` abgeschlossen.

- Nach Disconnect: `DISCONNECTED`, `configured=1`, `stored=0`, `auto_retry=0`,
  `attempts=1`, `links=1`, `epoch=4`, `rssi_valid=0`.
- Nach Connect: `LINK_UP`, `error=OK`, `configured=1`, `auto_retry=1`,
  `attempts=2`, `links=2`, `epoch=5`, `rssi_valid=1`, RSSI −38 dBm.
- Die SSID blieb unverändert im RAM; `last_link_error=0`, `failed_attempt=0`.

Damit sind manuelles Trennen und erneutes Verbinden mit dem erhaltenen RAM-Profil
am Pico nachgewiesen. Der nach Disconnect ausgegebene RSSI-Zahlenwert ist wegen
`rssi_valid=0` nur ein alter Messwert, kein aktueller Empfangswert.
Eine längere Beobachtung auf ausbleibende automatische Versuche nach Disconnect
wurde nicht separat protokolliert. Automatische Erholung nach AP-Ausfall,
Dauerlauf und Profilerhalt nach Stromverlust bleiben offen.

## Automatische Wiederverbindung am 08.10.2026, 23:29 Uhr (Europe/Berlin)

Im Anschluss an die Testanweisung (AP ausschalten, wieder einschalten, kein
manuelles Connect) übermittelt der Nutzer folgende zwei Zustände. Netzwerk-
Identifikatoren sind im öffentlichen Bericht ausgelassen.

| Wert | AP nicht verfügbar | Nach Wiederkehr des AP |
| --- | --- | --- |
| Zustand / aktueller Fehler | `RETRY_WAIT` / `NONET` | `LINK_UP` / `OK` |
| Automatische Wiederholung | 1 | 1 |
| Versuche / erfolgreiche Links | 7 / 2 | 10 / 3 |
| Epoch | 16 | 21 |
| RSSI gültig | 0 | 1, −40 dBm |
| Letzter negativer Linkstatus / Versuch | −2 / 7 | −1 / 9 |
| Profil | im RAM, nicht gespeichert | im RAM, nicht gespeichert |

Damit ist die automatische Erholung nach AP-Ausfall in diesem Hardwaretest
bestätigt. Der dritte Link wurde im zehnten Verbindungsversuch aufgebaut.
`last_link_error=-1` und `failed_attempt=9` bleiben absichtlich als Fehlerhistorie
stehen; sie widersprechen dem aktuellen `LINK_UP`/`error=OK` nicht.
Eine konkrete Wiederverbindungsdauer wurde nicht protokolliert.

W1/W2-Hauptabläufe sind nun am Pico belegt: Scan, RAM-Profil, erster Join,
manuelles Disconnect/Connect und automatische Erholung nach AP-Ausfall.
Dauerlauf, weitere Fehlerfälle und echte Watchdog-Fehlerinjektion bleiben offen.
Nächster Entwicklungsschritt ist W3: Ethernet-Rohframes über einen begrenzten
USB-Testtransport senden/empfangen und gegen eine LAN-Gegenstelle prüfen.
Dauerhafte Profile folgen in W4; Amiga-Bustests benötigen weiterhin M0.
