amiga-stumpi/funkotto/docs/results/2026-10-08-firmware-m1.md

# Pico-Firmware M1 – Prüfstand vom 08.10.2026

M1 (`0.1.0-m1`) ist die erste USB-Diagnose-Firmware. Die GPIOs werden vor USB
initialisiert, beide Bustreiber bleiben gesperrt. Drei Diagnosebefehle und ein
8-s-Watchdog sind implementiert. Es gibt noch keine WLAN-/Profilfunktion, kein
Parallelport-Protokoll und keinen Amiga-Treiber. Anleitung: [firmware/README.md](../../firmware/README.md).

## Geprüft

| Prüfung | Ergebnis |
| --- | --- |
| Aktuelles PCB gegen Firmware-GPIOs, Resetpfad, Freigabegatter und Pulldowns | bestanden |
| C-Hosttests der tatsächlichen GPIO-/Parserquellen mit ASan/UBSan | bestanden |
| Parsergrenzen, Überlauf, Binäreingaben, 100.000 Pseudozufallsbytes | bestanden |
| Sechs Python-Artefakttests einschließlich ungültiger UF2-Blöcke | bestanden |
| Arm-Release-Build für Pico 2 W, SDK 2.2.0 | bestanden |
| Zweiter Build aus separatem Quellverzeichnis | UF2 und BIN bytegleich |
| ELF-/UF2-Adressprüfung, Profilreserve, separater E10-Sektor, kein UART | bestanden |
| Grundstart, USB-Status und Kaltstart ohne Terminal auf realem Pico | durch Nutzer am 08.10.2026 bestätigt |
| Watchdog-Fehlerinjektion und elektrische Pegel/Trägerreset | noch nicht getestet |
| GitHub Actions | Build, Hosttests, Hardware-/Artefaktprüfung und Artefakt-Upload erfolgreich |

Referenzwerkzeuge: Arm GCC 13.2.1 (20231009), CMake 3.31.6, Ninja-Paket
1.11.1.4. Die genauen SDK-/Submodul-/Werkzeugpins stehen in
[dependencies.json](../../firmware/dependencies.json).
Die lokalen C-Tests benötigen `ASAN_OPTIONS=detect_leaks=0`, da LeakSanitizer in
dieser Ausführungsumgebung nicht auf `/proc` zugreifen kann. ASan/UBSan sind
aktiv; der getestete Anwendungscode verwendet keine Heap-Allokationen.

Die zwei verglichenen Builds verwenden die Kandidatenkennung `m1-candidate-20261008`:

- UF2 SHA-256: `4e44239ce33592092bed758b1d6ece83b52da6c36b5cc6348cb0de3711e54288`
- BIN SHA-256: `066a1abd13ac3b3bc19a3bbe1a956ac0c03f128820dfb3d93ca2b011694b0c2f`
- Firmware-Flashbereich: `0x10000000` bis exklusiv `0x10007800` (30.720 Byte).
- Zusätzlich ein E10-Kompatibilitätsblock bei `0x103FDF00` im reservierten Sektor.
- Die letzten 8192 Flashbytes ab `0x103FE000` bleiben unbeschrieben.

Ein anschließender Build mit der Quellcommit-ID besitzt erwartungsgemäß andere
Prüfsummen. Für jedes ausgelieferte Paket sind Kennung und Prüfsummen in seinem
`manifest.json` maßgeblich. Bitidentische Debug-Dateien oder identische Ergebnisse
mit beliebigen Toolchainversionen werden nicht behauptet.

Hardwarebasis: unveränderter Nutzerimport `d47ea64065e99507edfb3ae9dc4aa1727e00eb0b`,
PCB SHA-256 `b2f32df78c15e37ceb1bc0433f0356848106e7a86a1e82df63c3da5a7e26928c`.
Die vorhandenen älteren DRC-/ERC-Berichte gelten weiterhin nur für den damaligen B2-Stand.

## Nächste Abnahme

USB-Status und Kaltstart ohne Terminal sind nun bestätigt. Watchdog-Fehlerinjektion
und M0-Messungen am Träger bleiben offen. Aktive Amiga-Bustests bleiben bis M0
gesperrt. Die isolierte WLAN-Entwicklung folgt dem
[WLAN-Entwicklungsplan](../wlan-entwicklungsplan.md).

## GitHub-CI-Nachweis

[Actions-Lauf 37795325398](https://github.com/amiga-stumpi/funkotto/actions/runs/37795325398)
für Quellcommit `ae67bce3b2dc77c9185d60597cdf6d4c2a8bcbae` endete am
08.10.2026 um 14:48 UTC erfolgreich. Der Lauf baut aus einem frischen GitHub-Checkout
und stellt UF2, ELF, BIN, MAP und Manifest als `funkotto-m1-pico2w` bereit.
Das ist ein Software-Prüfnachweis; ein realer Pico wurde dabei nicht getestet.

## Nutzerbestätigung vom 08.10.2026, 21:54 Uhr (Europe/Berlin)

Vom Nutzer übermittelte erste Ausgabe:

```text
uptime_ms=28594 safe_init_us=148 bus_locked=1 output_mask=0x00700000 watchdog_boot=0 config_offset=0x003fe000
```

Nach Kaltstart:

```text
uptime_ms=17265 safe_init_us=148 bus_locked=1 output_mask=0x00700000 watchdog_boot=0 config_offset=0x003fe000
```

Der Nutzer bestätigte ausdrücklich: „Ja, das war der Kaltstart ohne geöffnetes Terminal.“
Damit sind realer Start, spätere USB-Statusabfrage und Start ohne Terminal nachgewiesen.
Die Ausgaben entsprechen dem erwarteten M1-GPIO-Zustand. `watchdog_boot=0` bestätigt
keinen Watchdog-Funktionstest; `safe_init_us=148` ist keine Messung ab Versorgung.
Keine elektrische Messung von OE_N/RUN oder aktiver Amiga-Test erfolgt.
Die Tests gehören zur hier besprochenen M1-Firmware; ein erneuter `info`-Auszug
mit Quellkennung wurde nicht übermittelt.
